not-forest/osu-taiko-drum/src/usb.rs

//! USB Device configuration and management.

use usbd_hid::hid_class::HIDClass;
use usb_device::{
    bus::UsbBusAllocator, 
    device::{StringDescriptors, UsbDevice, UsbDeviceBuilder, UsbDeviceState, UsbVidPid}, 
    LangID
};

use core::marker::PhantomData;
use super::pac::{RCC, USB, GPIOA};
use lhash::md5;

use super::hid::*;
use super::prog::Programmer;

/* Constant USB definitions. See: https://github.com/obdev/v-usb/blob/master/usbdrv/USB-IDs-for-free.txt */
const USB_VID: u16 = 0x16c0;
const USB_PID: u16 = 0x27db;
const USB_MANUFACTURER: &'static str = "Serhii Shkliaiev [not-forest]";
const USB_PRODUCT: &'static str = "Taiko Drum Controller";
const USB_SERIAL_NUMBER: &'static str = 
    unsafe { 
        core::str::from_utf8_unchecked(
            // USB serial number is generates on each build in form of md5 hash.
            md5(crate::version::TAIKO_HID_FIRMWARE_VERSION.as_bytes()).as_slice()
        )
    }; 
const USB_HID_CLASS_POLLING_MS: u8 = 60;

/// Usb VID-PID Pair
const TAIKO_DRUM_VIDPID: UsbVidPid  = UsbVidPid(USB_VID, USB_PID);

pub(crate) type UsbBus = stm32_usbd::UsbBus<UsbControllerSTM32F103>;
pub(crate) type UsbAllocator = UsbBusAllocator<UsbBus>;

/// Main USB communication structure for Taiko Drum.
///
/// Utilizes STM's USB peripheral to send HID reports for cross-platform compatibility and a serial
/// commication for desktop application.
pub struct UsbTaikoDrum<'a> {
    /// Physical USB device wrapper.
    pub(crate) dev: UsbDevice<'a, UsbBus>,
    /// HID Class for simulating a USB keyboard clicks.
    pub(crate) hid_keyboard: HIDClass<'a, UsbBus>,
    /// Serial interface programmer.
    pub(crate) programmer: Programmer<'a>,
    _phantom: PhantomData<USB>,
}

impl<'a> UsbTaikoDrum<'a> {
    /// Initializes a new instance of [`UsbTaikoDrum`].
    pub(crate) fn new(
        alloc: &'a Option<UsbAllocator>, 
        programmer: Programmer<'a>,
        usb: USB, 
        gpioa: &mut GPIOA, 
        rcc: &mut RCC
    ) -> Self {
        drop(usb);
        /* Configuring USB lines. */
        rcc.apb2enr.modify(|_, w| w.iopaen().set_bit());
        rcc.cfgr.modify(|_, w|
            w.ppre1().div4()        // Clock prescaler for low-freq area (18 MHz). 
             .usbpre().clear_bit()  // Divides SYSCLK by 1.5 to obtain 48 MHz.
            /* USB peripheral requires PCLK1 frequency to be greater than 8MHz. */
        );

        Self::reset(gpioa);

        log::info!("Preparing HID descriptor with polling speed of {} ms.", USB_HID_CLASS_POLLING_MS);
        /* Building HID classes for communication with host machine. */
        let hid_keyboard = HIDClass::new(
            alloc.as_ref().expect("Won't panic if this function is only called once."), 
            DrumHitStrokeHidReport::desc(), 
            USB_HID_CLASS_POLLING_MS
        );

        /* Initializing the USB device. */
        let dev = UsbDeviceBuilder::new(
            alloc.as_ref().expect("Won't panic if this function is only called once."),
            TAIKO_DRUM_VIDPID
        )
            .strings(&[
                StringDescriptors::new(LangID::EN)
                    .manufacturer(USB_MANUFACTURER)
                    .product(USB_PRODUCT)
                    .serial_number(USB_SERIAL_NUMBER)
            ]).expect("Shall not panic as long as data type is correct.")
            .supports_remote_wakeup(false)
            .device_release(crate::version::TAIKO_HID_FIRMWARE_VERSION_BCD)
            .device_class(0x03)
            .build();

        Self { dev, hid_keyboard, programmer, _phantom: PhantomData }
    }

    /// Simulates a USB disconnection by pulling down the D+ line.
    pub(crate) fn reset(gpioa: &mut GPIOA) {
        /* Setting USB reset condition on D+ line. */
        gpioa.crh.write(|w| 
            w      /* Pulling the line LOW, which simulates disconnection */
             .mode12().output()
             .cnf12().push_pull()
        );
        gpioa.odr.write(|w| w.odr12().clear_bit());
        cortex_m::asm::delay(720_000);

        gpioa.crh.write(|w| 
            w      /* Sets to floating input. */
             .mode11().input()
             .mode12().input()
             .cnf11().open_drain()
             .cnf12().open_drain()
        );
    }

    /// Polling function wrapper.
    pub(crate) fn poll(&mut self) {
        self.dev.poll(&mut [&mut self.hid_keyboard, &mut self.programmer.serial]);
    }

    /// First long poll that must be performed during enumeration.
    ///
    /// Halts the execution until the device state will be changed to configured.
    pub(crate) fn init_poll(&mut self) {
        // Locking on polling until device will be fully configured.
        if self.dev.state() == UsbDeviceState::Default {
            rtic::export::interrupt::free(|_| {
                while self.dev.state() != UsbDeviceState::Addressed { self.poll() }
                log::info!("USB device obtained it's address.");
                while self.dev.state() != UsbDeviceState::Configured { self.poll() }
                log::info!("USB device is fully configured by the host machine.");
            });
        }
    }
}

/// Marker microcontroller-dependent structure.
pub(crate) struct UsbControllerSTM32F103;

unsafe impl Sync for UsbControllerSTM32F103 {}

unsafe impl stm32_usbd::UsbPeripheral for UsbControllerSTM32F103 {
    const REGISTERS: *const () = USB::ptr() as *const ();
    const DP_PULL_UP_FEATURE: bool = false;
    const EP_MEMORY: *const () = 0x4000_6000 as _;
    const EP_MEMORY_ACCESS_2X16: bool = false;
    const EP_MEMORY_SIZE: usize = 512;

    fn enable() {
        let rcc = unsafe { &*RCC::ptr() };

        cortex_m::interrupt::free(|_| {
            // Enables USB peripheral
            rcc.apb1enr.modify(|_, w| w.usben().set_bit());

            // Resets USB peripheral
            rcc.apb1rstr.modify(|_, w| w.usbrst().set_bit());
            rcc.apb1rstr.modify(|_, w| w.usbrst().clear_bit());
        });
    }

    fn startup_delay() {
        // There is a chip specific startup delay. For STM32F103xx it's 1µs and this should wait for
        // at least that long.
        cortex_m::asm::delay(72);
    }
}
